0kouhj/ASC_Winter_Training_Camp/Mechanical/v2.0/STL打印文件/小车 - 电机固定件-1.STL

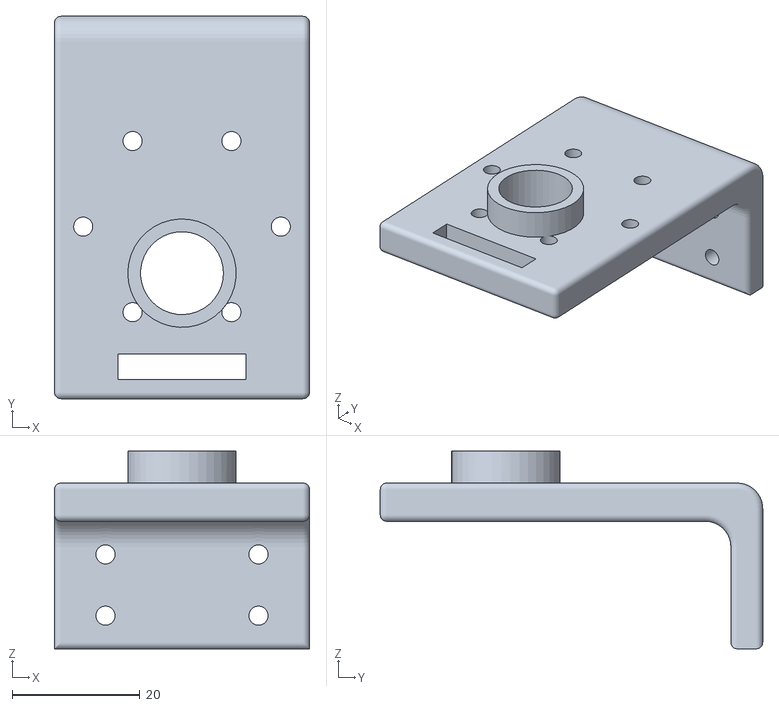
[picture p13: CAD file, 2026-01-29]
Mechanical/v2.0/STL打印文件/小车 - 电机固定件-1.STL
40.0 x 60.0 x 31.0
