0kouhj/ASC_Winter_Training_Camp/Mechanical/v2.0/STL打印文件/小车 - 插销-1.3mf

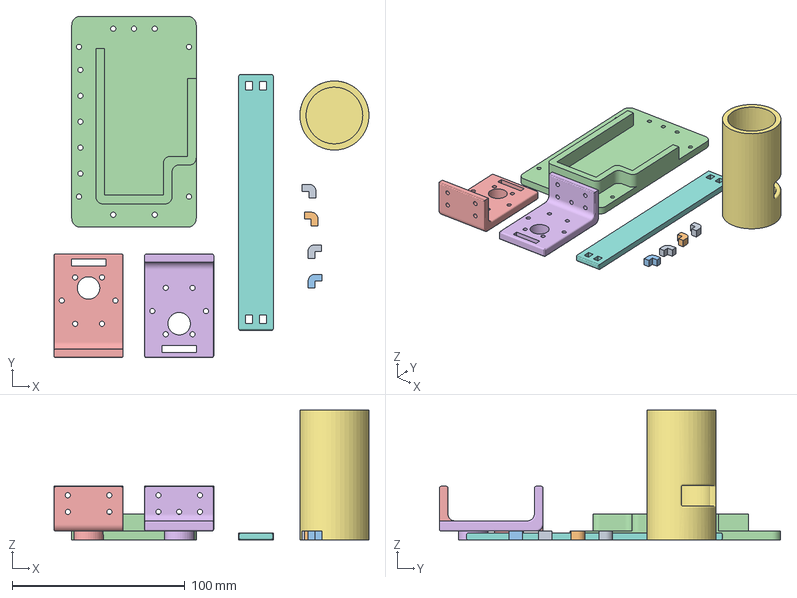
[picture p14: CAD file, 2026-01-29]
Mechanical/v2.0/STL打印文件/小车 - 插销-1.3mf
182.2 x 197.5 x 75.0 mm
小车 - 插销-1.STL
小车 - 插销-2.STL x 2
小车 - 插销-5.STL
小车 - 底板-2.STL
小车 - 电机固定件-1.STL
小车 - 电机固定件-2.STL
小车 - 电机套筒-1.STL
小车 - 电机下固定板-1.STL
