0kouhj/ASC_Winter_Training_Camp/Mechanical/v2.0/电机套筒.SLDPRT

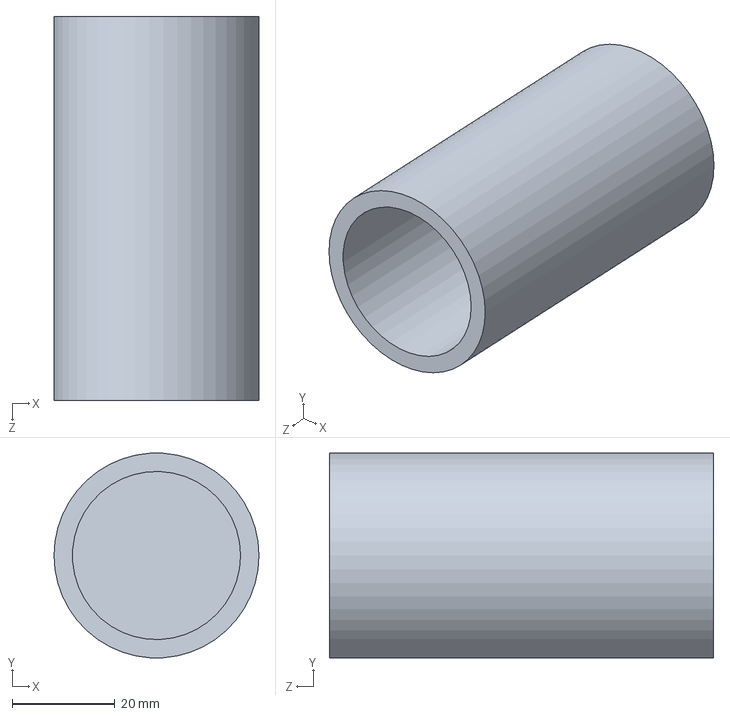
[picture p15: CAD file, 2026-01-29]
Mechanical/v2.0/电机套筒.SLDPRT
40.0 x 39.9 x 75.0 mm
