0kouhj/ASC_Winter_Training_Camp/Mechanical/v2.0/电机后半部分.stp

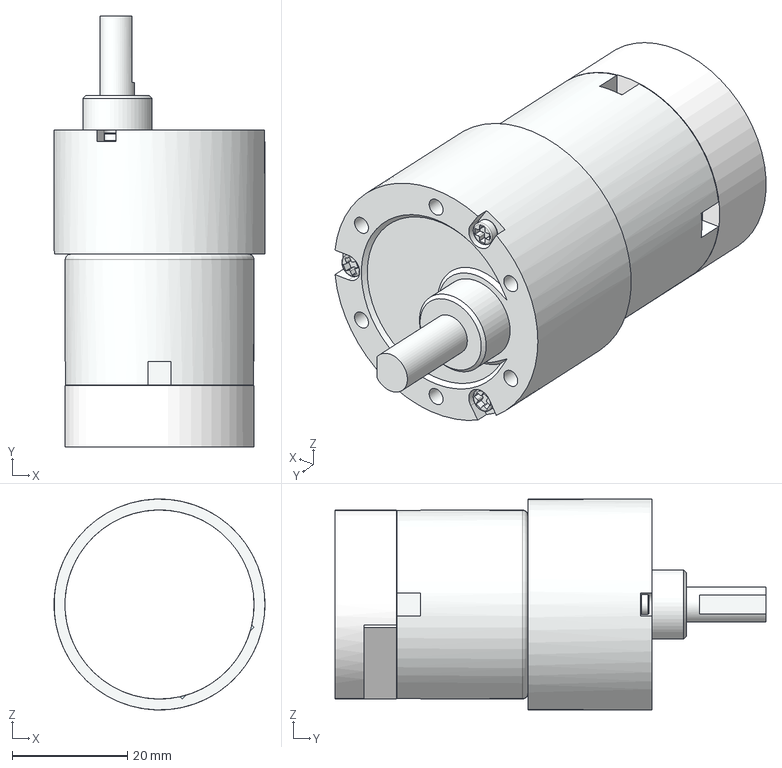
[picture p16: CAD file, 2026-01-19]
Mechanical/v2.0/电机后半部分.stp
36.6 x 74.8 x 36.6 mm
