0kouhj/ASC_Winter_Training_Camp/Firmware/project/user/src/isr.c

/*********************************************************************************************************************
 * MM32F327X-G8P Opensourec Library 即（MM32F327X-G8P 开源库）是一个基于官方 SDK 接口的第三方开源库
 * Copyright (c) 2022 SEEKFREE 逐飞科技
 *
 * 本文件是 MM32F327X-G8P 开源库的一部分
 *
 * MM32F327X-G8P 开源库 是免费软件
 * 您可以根据自由软件基金会发布的 GPL（GNU General Public License，即 GNU通用公共许可证）的条款
 * 即 GPL 的第3版（即 GPL3.0）或（您选择的）任何后来的版本，重新发布和/或修改它
 *
 * 本开源库的发布是希望它能发挥作用，但并未对其作任何的保证
 * 甚至没有隐含的适销性或适合特定用途的保证
 * 更多细节请参见 GPL
 *
 * 您应该在收到本开源库的同时收到一份 GPL 的副本
 * 如果没有，请参阅<https://www.gnu.org/licenses/>
 *
 * 额外注明：
 * 本开源库使用 GPL3.0 开源许可证协议 以上许可申明为译文版本
 * 许可申明英文版在 libraries/doc 文件夹下的 GPL3_permission_statement.txt 文件中
 * 许可证副本在 libraries 文件夹下 即该文件夹下的 LICENSE 文件
 * 欢迎各位使用并传播本程序 但修改内容时必须保留逐飞科技的版权声明（即本声明）
 *
 * 文件名称          isr
 * 公司名称          成都逐飞科技有限公司
 * 版本信息          查看 libraries/doc 文件夹内 version 文件 版本说明
 * 开发环境          IAR 8.32.4 or MDK 5.37
 * 适用平台          MM32F327X_G8P
 * 店铺链接          https://seekfree.taobao.com/
 *
 * 修改记录
 * 日期              作者                备注
 * 2022-08-10        Teternal            first version
 ********************************************************************************************************************/

#include "isr.h"
#include "Simple_Timewheel.h"
#include "bsp_motor.h"
#include "bsp_encoder.h"
#include "Control.h"
#include "bsp_imu.h"

extern volatile uint8_t tick_flag;
//-------------------------------------------------------------------------------------------------------------------
// 函数简介     TIM1 的定时器更新中断服务函数 启动 .s 文件定义 不允许修改函数名称
//              默认优先级 修改优先级使用 interrupt_set_priority(TIM1_UP_IRQn, 1);
//-------------------------------------------------------------------------------------------------------------------
void TIM1_UP_IRQHandler(void)
{
    // 此处编写用户代码

    // 此处编写用户代码
    TIM1->SR &= ~TIM1->SR; // 清空中断状态
}

//-------------------------------------------------------------------------------------------------------------------
// 函数简介     TIM2 的定时器中断服务函数 启动 .s 文件定义 不允许修改函数名称
//              默认优先级 修改优先级使用 interrupt_set_priority(TIM2_IRQn, 1);
//-------------------------------------------------------------------------------------------------------------------
void TIM2_IRQHandler(void)
{
    // 此处编写用户代码

    // 此处编写用户代码
    TIM2->SR &= ~TIM2->SR; // 清空中断状态
}

//-------------------------------------------------------------------------------------------------------------------
// 函数简介     TIM3 的定时器中断服务函数 启动 .s 文件定义 不允许修改函数名称
//              默认优先级 修改优先级使用 interrupt_set_priority(TIM3_IRQn, 1);
//-------------------------------------------------------------------------------------------------------------------
void TIM3_IRQHandler(void)
{
    // 此处编写用户代码

    // 此处编写用户代码
    TIM3->SR &= ~TIM3->SR; // 清空中断状态
}

//-------------------------------------------------------------------------------------------------------------------
// 函数简介     TIM4 的定时器中断服务函数 启动 .s 文件定义 不允许修改函数名称
//              默认优先级 修改优先级使用 interrupt_set_priority(TIM4_IRQn, 1);
//-------------------------------------------------------------------------------------------------------------------
void TIM4_IRQHandler(void)
{
    // 此处编写用户代码

    // 此处编写用户代码
    TIM4->SR &= ~TIM4->SR; // 清空中断状态
}

//-------------------------------------------------------------------------------------------------------------------
// 函数简介     TIM5 的定时器中断服务函数 启动 .s 文件定义 不允许修改函数名称
//              默认优先级 修改优先级使用 interrupt_set_priority(TIM5_IRQn, 1);
//-------------------------------------------------------------------------------------------------------------------
void TIM5_IRQHandler(void)
{
    // 此处编写用户代码

    // 此处编写用户代码
    TIM5->SR &= ~TIM5->SR; // 清空中断状态
}

//-------------------------------------------------------------------------------------------------------------------
// 函数简介     TIM6 的定时器中断服务函数 启动 .s 文件定义 不允许修改函数名称
//              默认优先级 修改优先级使用 interrupt_set_priority(TIM6_IRQn, 1);
//-------------------------------------------------------------------------------------------------------------------
void TIM6_IRQHandler(void)
{
    if (sys_ready){
        // 此处编写用户代码
        static uint8_t count = 0;
        count++;
        if (count >= 5)
        {
            ICM_Update();
            count = 0;
        }
        else
        {
            ICM_Update_Gyro_Only();
            fuck_imu++;
        }
        tick_flag = 1;
        Attitude_Update();
        Control_Loop_1ms(0,0);
        encoder_update();
        motor_update();
    }
    
    // 此处编写用户代码
    TIM6->SR &= ~TIM6->SR; // 清空中断状态
}

//-------------------------------------------------------------------------------------------------------------------
// 函数简介     TIM7 的定时器中断服务函数 启动 .s 文件定义 不允许修改函数名称
//              默认优先级 修改优先级使用 interrupt_set_priority(TIM7_IRQn, 1);
//-------------------------------------------------------------------------------------------------------------------
void TIM7_IRQHandler(void)
{
    // 此处编写用户代码
    if (sys_ready)
    {
        
        // 此处编写用户代码
    }
    // 此处编写用户代码
    TIM7->SR &= ~TIM7->SR; // 清空中断状态
}

//-------------------------------------------------------------------------------------------------------------------
// 函数简介     TIM8 的定时器更新中断服务函数 启动 .s 文件定义 不允许修改函数名称
//              默认优先级 修改优先级使用 interrupt_set_priority(TIM8_UP_IRQn, 1);
//-------------------------------------------------------------------------------------------------------------------
void TIM8_UP_IRQHandler(void)
{
    tsl1401_collect_pit_handler();
    // 此处编写用户代码

    // 此处编写用户代码
    TIM8->SR &= ~TIM8->SR; // 清空中断状态
}

//-------------------------------------------------------------------------------------------------------------------
// 函数简介     UART1 的串口中断服务函数 启动 .s 文件定义 不允许修改函数名称
//              默认优先级 修改优先级使用 interrupt_set_priority(UART1_IRQn, 1);
//-------------------------------------------------------------------------------------------------------------------
void UART1_IRQHandler(void)
{
    if (UART1->ISR & 0x00000001) // 串口发送缓冲空中断
    {
        // 此处编写用户代码
        // 务必填写数据或者关闭中断 否则会一直触发串口发送中断

        // 此处编写用户代码
        UART1->ICR |= 0x00000001; // 清除中断标志位
    }
    if (UART1->ISR & 0x00000002) // 串口接收缓冲中断
    {
#if DEBUG_UART_USE_INTERRUPT       // 如果开启 debug 串口中断
        debug_interrupr_handler(); // 调用 debug 串口接收处理函数 数据会被 debug 环形缓冲区读取
#endif                             // 如果修改了 DEBUG_UART_INDEX 那这段代码需要放到对应的串口中断去
        // 此处编写用户代码
        // 务必读取数据或者关闭中断 否则会一直触发串口接收中断

        // 此处编写用户代码
        UART1->ICR |= 0x00000002; // 清除中断标志位
    }
}

//-------------------------------------------------------------------------------------------------------------------
// 函数简介     UART2 的串口中断服务函数 启动 .s 文件定义 不允许修改函数名称
//              默认优先级 修改优先级使用 interrupt_set_priority(UART2_IRQn, 1);
//-------------------------------------------------------------------------------------------------------------------
void UART2_IRQHandler(void)
{
    if (UART2->ISR & 0x00000001) // 串口发送缓冲空中断
    {
        // 此处编写用户代码
        // 务必填写数据或者关闭中断 否则会一直触发串口发送中断

        // 此处编写用户代码
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
void DMA2_Channel5_IRQHandler(void)
{
    if (DMA2->ISR & (0x00000001 << (4 * 4))) // 判断触发通道
    {
        // 此处编写用户代码

        // 此处编写用户代码
        DMA2->IFCR |= (0x00000001 << (4 * 4)); // 清空该通道中断标志
    }
}
