0kouhj/ASC_Winter_Training_Camp/Firmware/project/code/bsp_oled.h

#ifndef BSP_OLED_H
#define BSP_OLED_H

#include "zf_common_headfile.h"  // 修改为 MM32 的设备头文件
#include "OLED_Data.h"
#include <stdint.h>

/*参数宏定义*********************/

/*FontSize参数取值*/
/*此参数值不仅用于判断，而且用于计算横向字符偏移，默认值为字体像素宽度*/
#define OLED_8X16				8
#define OLED_6X8				6

/*IsFilled参数数值*/
#define OLED_UNFILLED			0
#define OLED_FILLED				1

/*********************参数宏定义*/


/*函数声明*********************/

/*初始化函数*/
void OLED_Init(void);

/*更新函数*/
void OLED_Update(void);
void OLED_UpdateArea(int16_t X, int16_t Y, uint8_t Width, uint8_t Height);

/*显存控制函数*/
void OLED_Clear(void);
void OLED_ClearArea(int16_t X, int16_t Y, uint8_t Width, uint8_t Height);
void OLED_Reverse(void);
void OLED_ReverseArea(int16_t X, int16_t Y, uint8_t Width, uint8_t Height);

/*显示函数*/
void OLED_ShowChar(int16_t X, int16_t Y, char Char, uint8_t FontSize);
void OLED_ShowString(int16_t X, int16_t Y, char *String, uint8_t FontSize);
void OLED_ShowNum(int16_t X, int16_t Y, uint32_t Number, uint8_t Length, uint8_t FontSize);
void OLED_ShowSignedNum(int16_t X, int16_t Y, int32_t Number, uint8_t Length, uint8_t FontSize);
void OLED_ShowHexNum(int16_t X, int16_t Y, uint32_t Number, uint8_t Length, uint8_t FontSize);
void OLED_ShowBinNum(int16_t X, int16_t Y, uint32_t Number, uint8_t Length, uint8_t FontSize);
void OLED_ShowFloatNum(int16_t X, int16_t Y, double Number, uint8_t IntLength, uint8_t FraLength, uint8_t FontSize);
void OLED_ShowImage(int16_t X, int16_t Y, uint8_t Width, uint8_t Height, const uint8_t *Image);
void OLED_Printf(int16_t X, int16_t Y, uint8_t FontSize, char *format, ...);

/*绘图函数*/
void OLED_DrawPoint(int16_t X, int16_t Y);
uint8_t OLED_GetPoint(int16_t X, int16_t Y);
void OLED_DrawLine(int16_t X0, int16_t Y0, int16_t X1, int16_t Y1);
void OLED_DrawRectangle(int16_t X, int16_t Y, uint8_t Width, uint8_t Height, uint8_t IsFilled);
void OLED_DrawTriangle(int16_t X0, int16_t Y0, int16_t X1, int16_t Y1, int16_t X2, int16_t Y2, uint8_t IsFilled);
void OLED_DrawCircle(int16_t X, int16_t Y, uint8_t Radius, uint8_t IsFilled);
void OLED_DrawEllipse(int16_t X, int16_t Y, uint8_t A, uint8_t B, uint8_t IsFilled);
void OLED_DrawArc(int16_t X, int16_t Y, uint8_t Radius, int16_t StartAngle, int16_t EndAngle, uint8_t IsFilled);

/*Test*/
void OLED_Test(void);
/*********************函数声明*/

/* 写引脚逻辑封装 */
#define OLED_W_SCL(x)       GPIO_WriteBit(OLED_SCL_PORT, OLED_SCL_PIN, (BitAction)(x))
#define OLED_W_SDA(x)       GPIO_WriteBit(OLED_SDA_PORT, OLED_SDA_PIN, (BitAction)(x))


#endif
