0kouhj/ASC_Winter_Training_Camp/Firmware/project/code/bsp_key.h

#ifndef BSP_KEY_H
#define BSP_KEY_H

#include "stdint.h"

// 按键索引
#define KEY_1                   0
#define KEY_2                   1
#define KEY_3                   2
#define KEY_4                   3
#define KEY_5                   4
#define KEY_6                   5

// 按键触发标志
#define KEY_HOLD                0x01
#define KEY_DOWN                0x02
#define KEY_UP                  0x04
#define KEY_SINGLE              0x08
#define KEY_DOUBLE              0x10
#define KEY_LONG                0x20
#define KEY_REPEAT              0x40

void KEY_Init(void);
uint8_t Key_Check(uint8_t n, uint8_t Flag);
void Key_Tick(void);
uint8_t Key_GetState(uint8_t n);

#endif
