0kouhj/ASC_Winter_Training_Camp/docs/MM32F327X_G8P_Library-master/Example/E11_interrupt_priority_set_demo/user/src/main.c

/*********************************************************************************************************************
* MM32F327X-G8P Opensourec Library 即（MM32F327X-G8P 开源库）是一个基于官方 SDK 接口的第三方开源库
* Copyright (c) 2022 SEEKFREE 逐飞科技
* 
* 本文件是 MM32F327X-G8P 开源库的一部分
* 
* MM32F327X-G8P 开源库 是免费软件
* 您可以根据自由软件基金会发布的 GPL（GNU General Public License，即 GNU通用公共许可证）的条款
* 即 GPL 的第3版（即 GPL3.0）或（您选择的）任何后来的版本，重新发布和/或修改它
* 
* 本开源库的发布是希望它能发挥作用，但并未对其作任何的保证
* 甚至没有隐含的适销性或适合特定用途的保证
* 更多细节请参见 GPL
* 
* 您应该在收到本开源库的同时收到一份 GPL 的副本
* 如果没有，请参阅<https://www.gnu.org/licenses/>
* 
* 额外注明：
* 本开源库使用 GPL3.0 开源许可证协议 以上许可申明为译文版本
* 许可申明英文版在 libraries/doc 文件夹下的 GPL3_permission_statement.txt 文件中
* 许可证副本在 libraries 文件夹下 即该文件夹下的 LICENSE 文件
* 欢迎各位使用并传播本程序 但修改内容时必须保留逐飞科技的版权声明（即本声明）
* 
* 文件名称          main
* 公司名称          成都逐飞科技有限公司
* 版本信息          查看 libraries/doc 文件夹内 version 文件 版本说明
* 开发环境          IAR 8.32.4 or MDK 5.37
* 适用平台          MM32F327X_G8P
* 店铺链接          https://seekfree.taobao.com/
* 
* 修改记录
* 日期              作者                备注
* 2022-08-10        Teternal            first version
********************************************************************************************************************/

#include "zf_common_headfile.h"

// 打开新的工程或者工程移动了位置务必执行以下操作
// 第一步 关闭上面所有打开的文件
// 第二步 project->clean  等待下方进度条走完


// *************************** 例程硬件连接说明 ***************************
// 核心板正常供电即可 无需额外连接


// *************************** 例程测试说明 ***************************
// 1.核心板烧录完成本例程，完成上电
// 
// 2.可以看到核心板上 H2 LED 闪烁
// 
// 3.将 KEY1 宏定义对应的引脚 按下对应主板按键或者从悬空状态接到 GND 可以看到 B13 LED 亮起 H2 LED 不再闪烁
// 
// 3.将 KEY1 宏定义对应的引脚 松开对应主板按键或者恢复悬空状态或者接到 VCC 可以看到 B13 LED 熄灭 H2 LED 恢复闪烁
// 
// 如果发现现象与说明严重不符 请参照本文件最下方 例程常见问题说明 进行排查


// **************************** 代码区域 ****************************
#define LED1                    (H2 )
#define LED2                    (B13)

#define PIT                     (TIM6_PIT )                                     // 使用的周期中断编号 如果修改 需要同步对应修改周期中断编号与 isr.c 中的调用
#define PIT_PRIORITY            (TIM6_IRQn)                                     // 对应周期中断的中断编号 在 mm32f3277gx.h 头文件中查看 IRQn_Type 枚举体

#define KEY                     (E2 )                                           // 使用的外部中断输入引脚 如果修改 需要同步对应修改外部中断编号与 isr.c 中的调用
#define KEY_EXTI                (EXTI2_IRQn)                                    // 对应外部中断的中断编号 在 mm32f3277gx.h 头文件中查看 IRQn_Type 枚举体

uint8 exti_state[4];

int main (void)
{
    clock_init(SYSTEM_CLOCK_120M);                                              // 初始化芯片时钟 工作频率为 120MHz
    debug_init();                                                               // 初始化默认 Debug UART

    // 此处编写用户代码 例如外设初始化代码等
    gpio_init(LED1, GPO, GPIO_HIGH, GPO_PUSH_PULL);                             // 初始化 LED1 输出 默认高电平 推挽输出模式
    gpio_init(LED2, GPO, GPIO_HIGH, GPO_PUSH_PULL);                             // 初始化 LED2 输出 默认高电平 推挽输出模式

    exti_init(KEY, EXTI_TRIGGER_FALLING);                                       // 初始化 KEY 为外部中断输入 下降沿触发
    interrupt_set_priority(KEY_EXTI, 0);                                        // 设置 KEY 对应外部中断的中断有先级为 0

    pit_ms_init(PIT, 200);                                                      // 初始化 PIT 为周期中断 1000ms 周期
    interrupt_set_priority(PIT_PRIORITY, 1);                                    // 设置 PIT 对周期中断的中断优先级为 1 优先级比外部中断低 会被外部中断打断
    // 此处编写用户代码 例如外设初始化代码等

    while(1)
    {
        // 此处编写需要循环执行的代码
        // 此处编写需要循环执行的代码
    }
}

//-------------------------------------------------------------------------------------------------------------------
// 函数简介     KEY 的按键外部中断处理函数 这个函数将在 KEY 引脚对应的外部中断调用 详见 isr.c
// 参数说明     void
// 返回参数     void
// 使用示例     key_exti_handler();
//-------------------------------------------------------------------------------------------------------------------
void key_exti_handler (void)
{
    gpio_set_level(LED2, 0);                                                    // 点亮核心板 B13 LED
    while(1)
    {
        if(1 == gpio_get_level(KEY))                                            // 松开按键 电压恢复默认上拉高电平
        {
            break;                                                              // 退出死循环
        }
    }
    gpio_set_level(LED2, 1);                                                    // 熄灭核心板 B13 LED
}

//-------------------------------------------------------------------------------------------------------------------
// 函数简介     PIT 的周期中断处理函数 这个函数将在 PIT 对应的定时器中断调用 详见 isr.c
// 参数说明     void
// 返回参数     void
// 使用示例     pit_handler();
//-------------------------------------------------------------------------------------------------------------------
void pit_handler (void)
{
    gpio_toggle_level(LED1);                                                    // 触发 PIT 中断后翻转 H2 LED 状态
}
// **************************** 代码区域 ****************************

// *************************** 例程常见问题说明 ***************************
// 遇到问题时请按照以下问题检查列表检查
// 
// 问题1：H2 LED 不闪烁
//      查看程序是否正常烧录，是否下载报错，确认正常按下复位按键
//      万用表测量对应 LED 引脚电压是否变化，如果不变化证明程序未运行，如果变化证明 LED 灯珠损坏
// 
// 问题2：KEY1 对应引脚接信号无 B13 LED 变化
//      如果使用主板测试，主板必须要用电池供电
//      万用表检查 KEY1 对应引脚电压是否正常变化，是否跟接入信号不符，引脚是否接错
